rcltech/sls/sls/src/images/LED_off.png

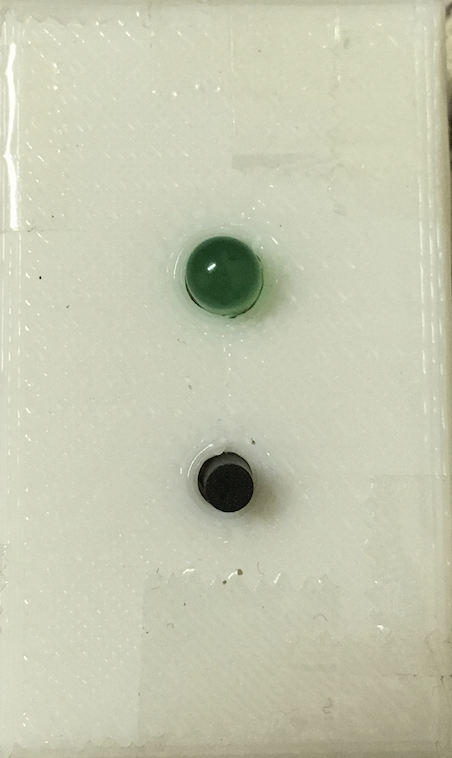
sls/src/images/LED_off.png
