rcltech/sls/sls/src/images/LED_on_pressed.png

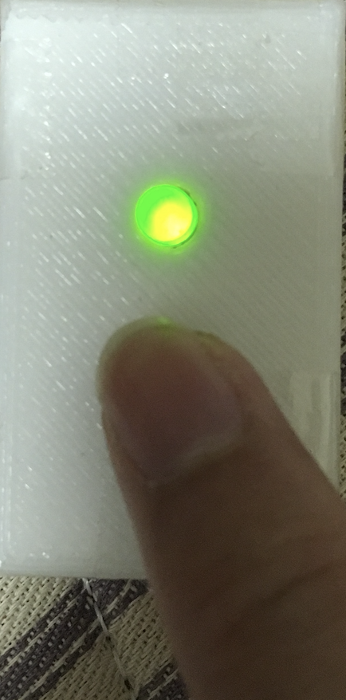
sls/src/images/LED_on_pressed.png
