rcltech/sls/sls/src/images/team-members/gela.png

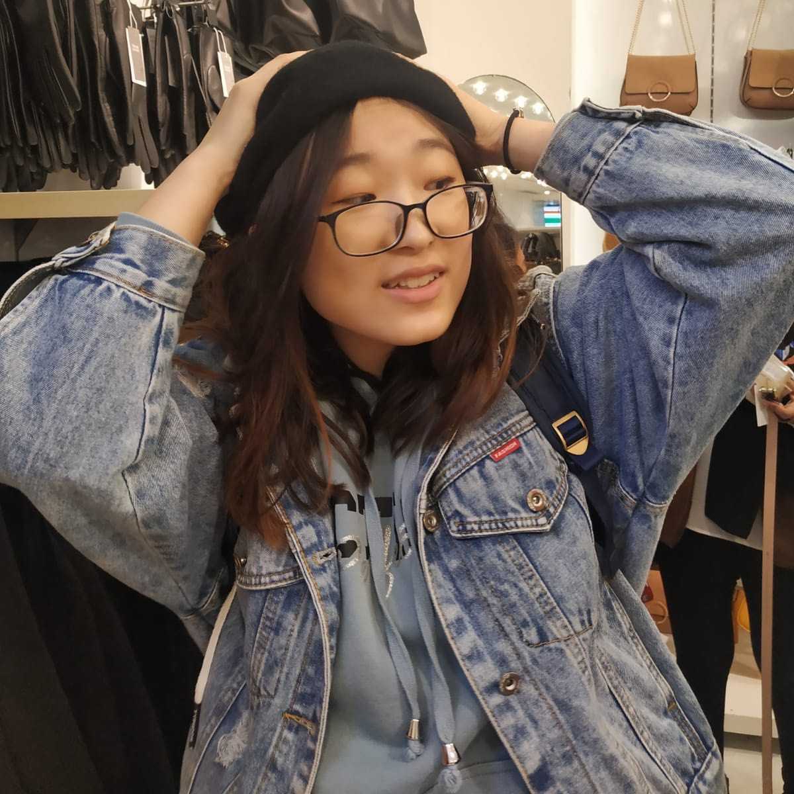
sls/src/images/team-members/gela.png
