rcltech/sls/sls/src/images/team-members/sean.jpg

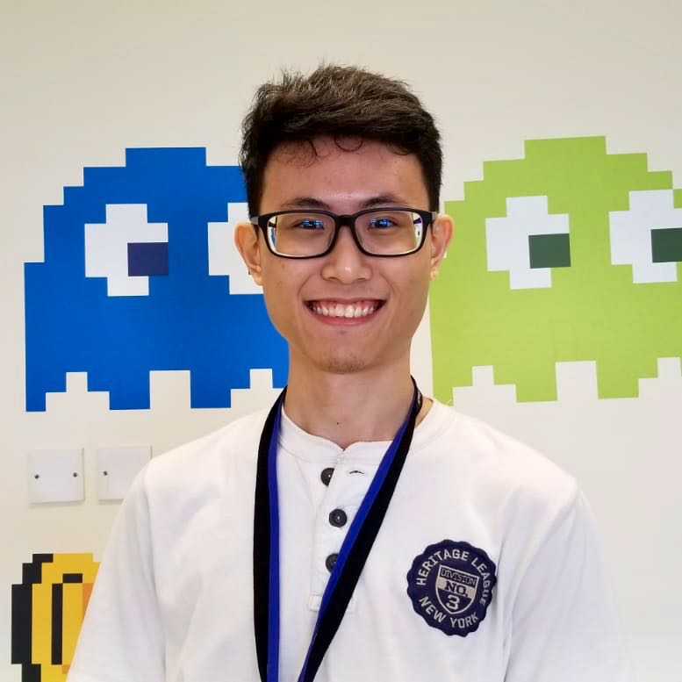
sls/src/images/team-members/sean.jpg
