rcltech/sls/sls/src/images/team-members/sid.png

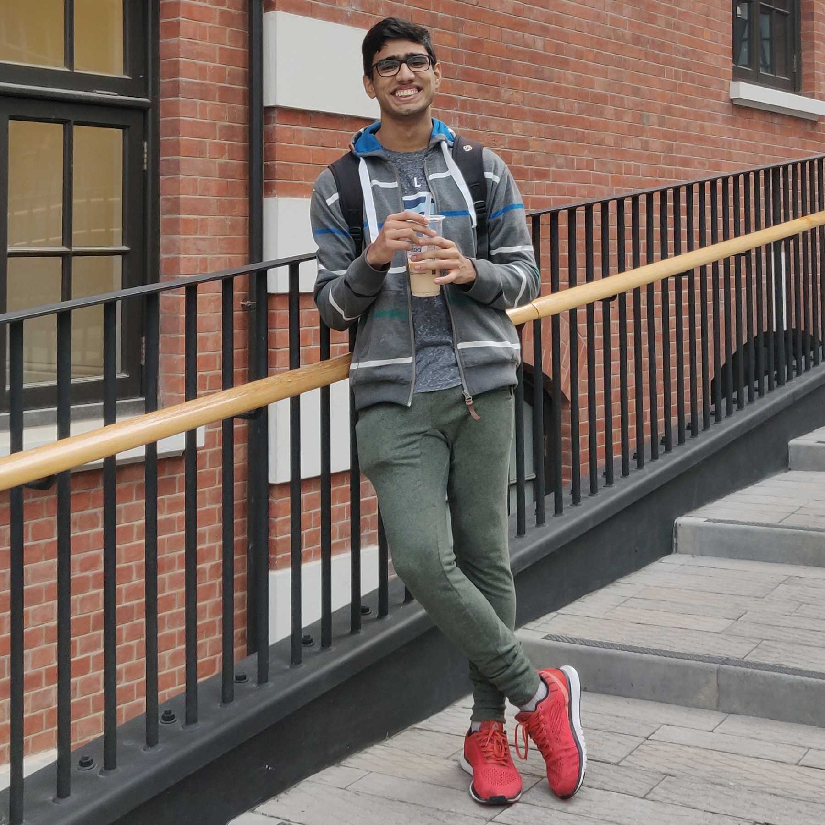
sls/src/images/team-members/sid.png
