rcltech/sls/sls/src/images/team-members/utkarsh.png

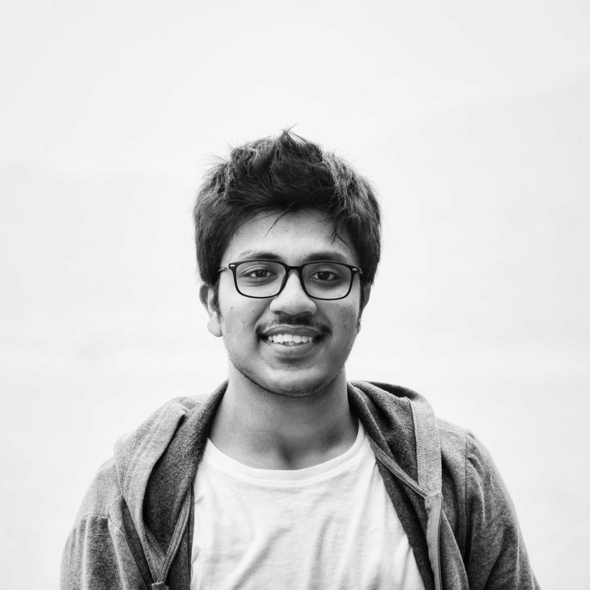
sls/src/images/team-members/utkarsh.png
