rcltech/sls/sls/src/images/unavailable.png

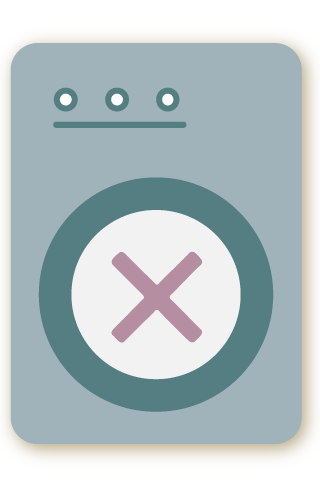
sls/src/images/unavailable.png
